MichaelNeas/3dhydra/assets/img/Daniel_DeMarco_Profile_Img.jpg

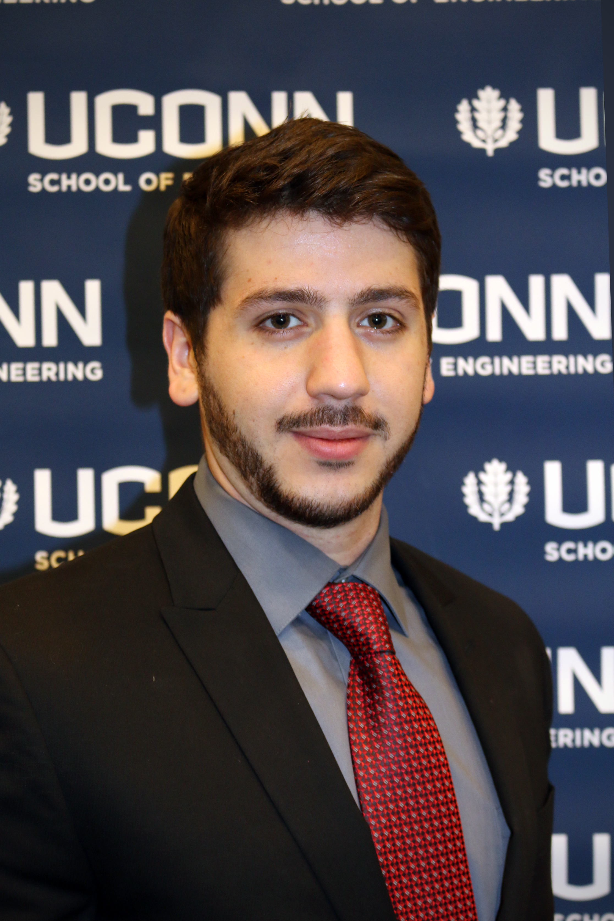
assets/img/Daniel_DeMarco_Profile_Img.jpg
