MichaelNeas/3dhydra/assets/img/Ted_Jenson_Profile_Img.jpg

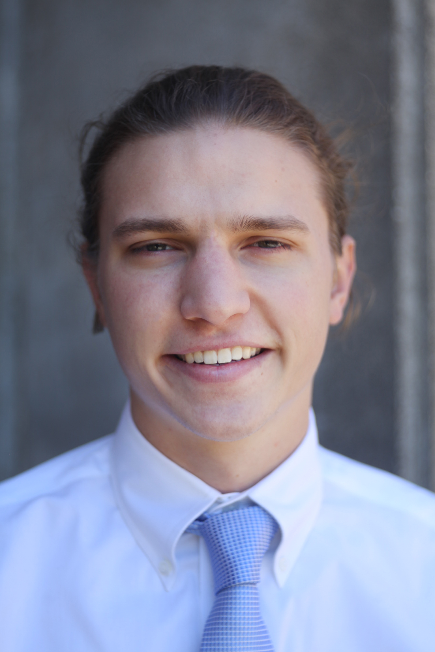
assets/img/Ted_Jenson_Profile_Img.jpg
