MichaelNeas/3dhydra/assets/stl/Hydra_-_middle_ringFingers-1_distal_middle-1.STL

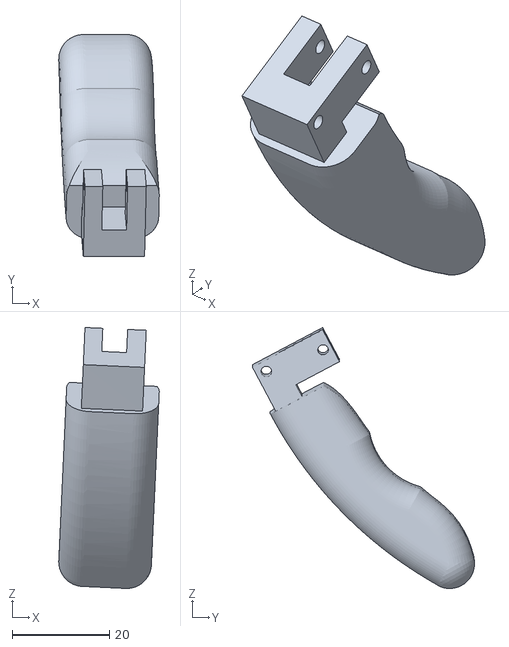
[picture p31: CAD file, 2016-04-29]
assets/stl/Hydra_-_middle_ringFingers-1_distal_middle-1.STL
20.7 x 45.6 x 53.6
