MichaelNeas/3dhydra/assets/stl/Hydra_-_pointerFinger-1_actuator-1.STL

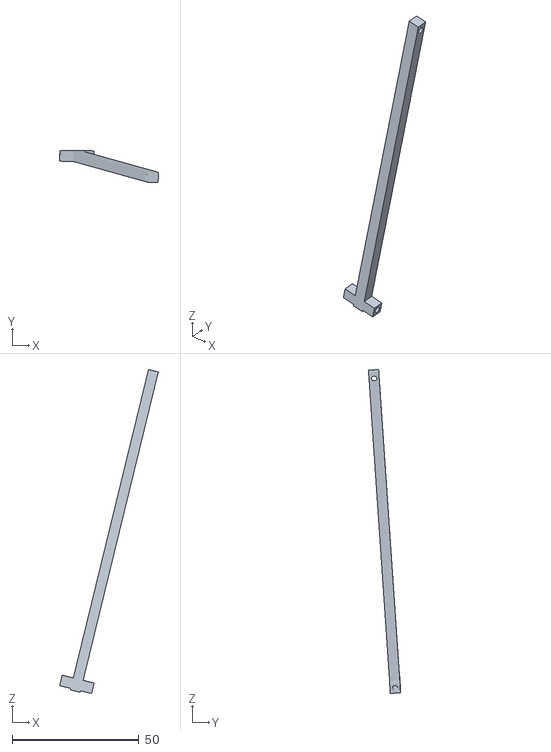
[picture p32: CAD file, 2016-04-29]
assets/stl/Hydra_-_pointerFinger-1_actuator-1.STL
38.9 x 12.6 x 127.7
