MichaelNeas/3dhydra/assets/stl/Hydra_-_middle_ringFingers-1_fingerREDUX-1.STL

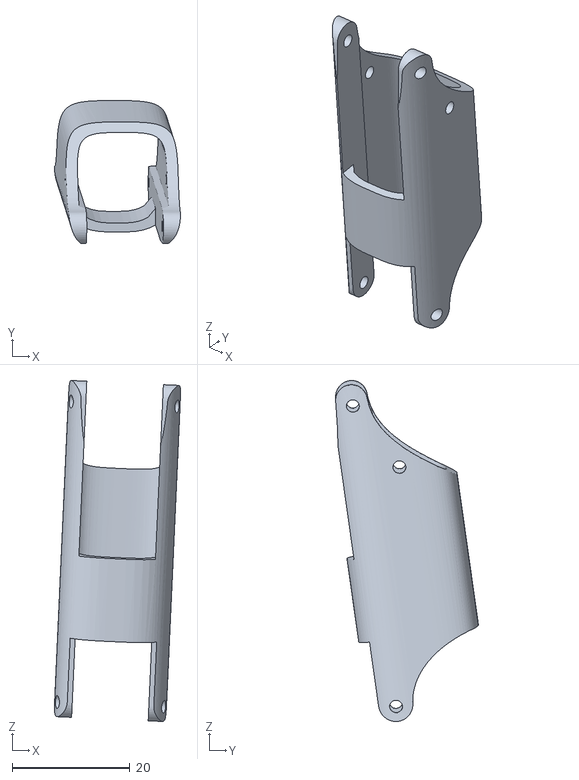
[picture p33: CAD file, 2016-04-29]
assets/stl/Hydra_-_middle_ringFingers-1_fingerREDUX-1.STL
21.4 x 24.2 x 57.8
