MichaelNeas/3dhydra/assets/stl/Hydra_-_pinkFinger-1_pinkyDM-1.STL

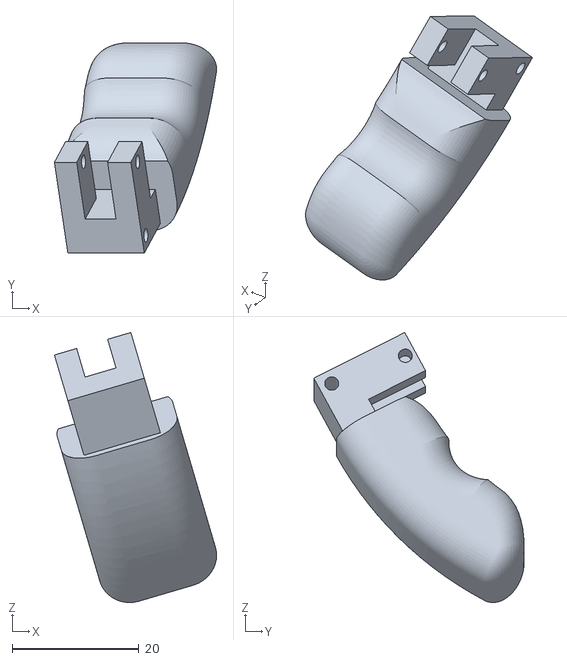
[picture p34: CAD file, 2016-04-29]
assets/stl/Hydra_-_pinkFinger-1_pinkyDM-1.STL
25.6 x 33.3 x 42.7
