MichaelNeas/3dhydra/assets/stl/Hydra_-_HydraForeArm-2_RackandPinion-1_ServoModel-1.STL

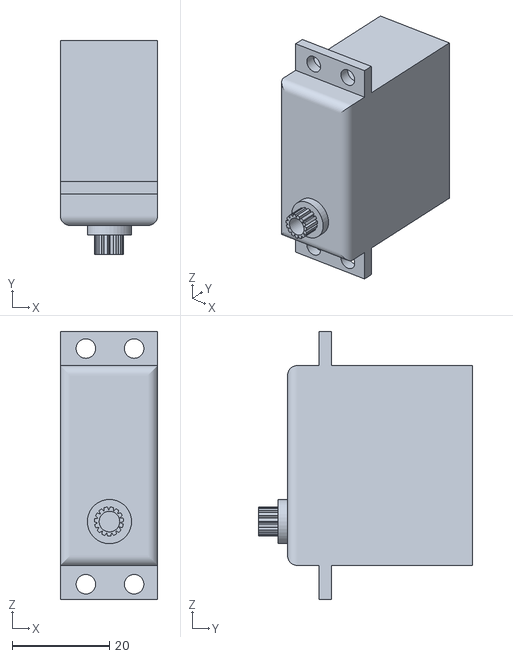
[picture p35: CAD file, 2016-04-29]
assets/stl/Hydra_-_HydraForeArm-2_RackandPinion-1_ServoModel-1.STL
20.0 x 44.0 x 55.0
