MichaelNeas/3dhydra/assets/stl/Hydra_-_HydraForeArm-2_arduinosHome-1.STL

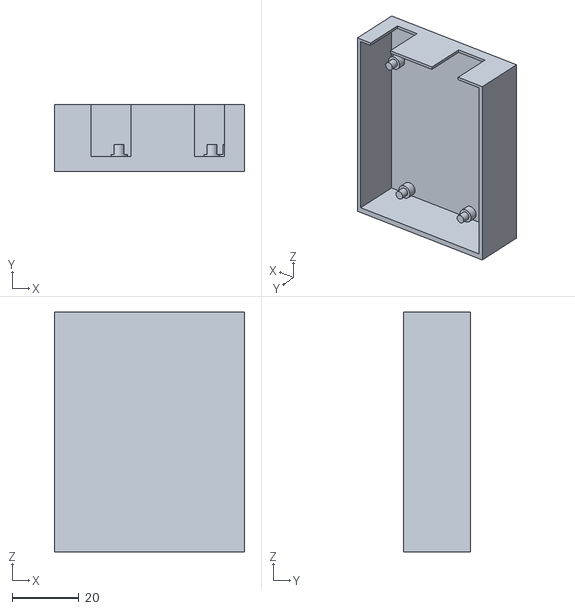
[picture p36: CAD file, 2016-04-29]
assets/stl/Hydra_-_HydraForeArm-2_arduinosHome-1.STL
57.0 x 20.0 x 72.0
