MichaelNeas/3dhydra/assets/stl/RackandPinion.STL

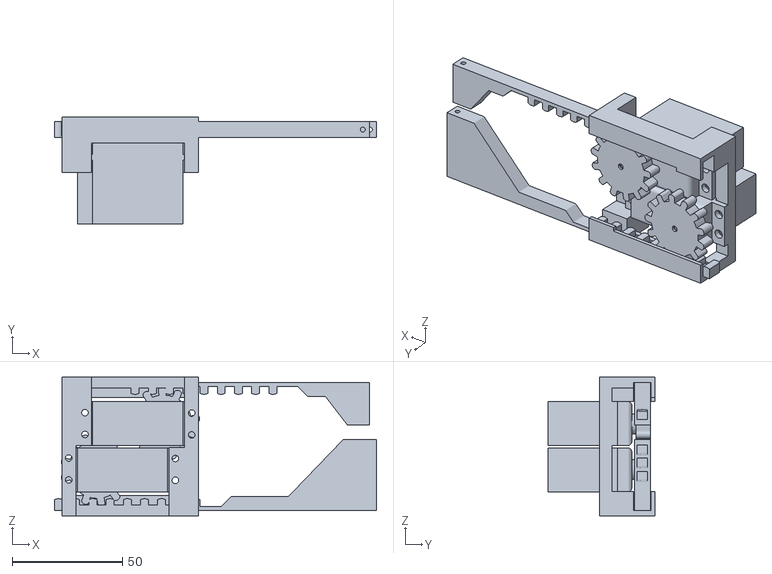
[picture p37: CAD file, 2016-04-29]
assets/stl/RackandPinion.STL
146.0 x 48.4 x 63.0
