MichaelNeas/3dhydra/assets/stl/Hydra_-_middle_ringFingers-1_middleActuator-1.STL

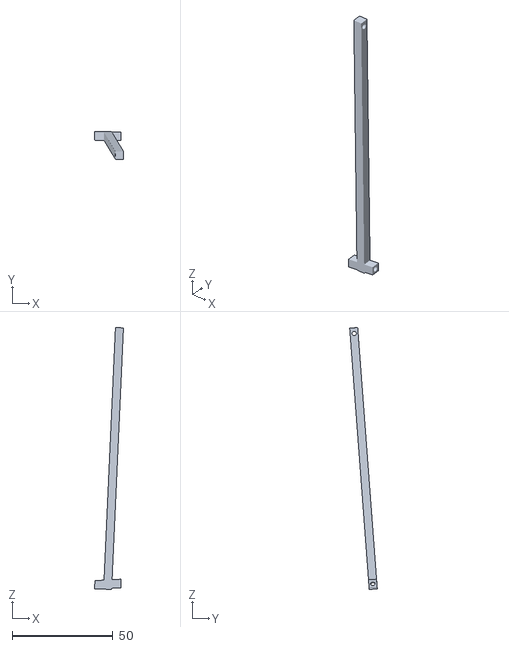
[picture p38: CAD file, 2016-04-29]
assets/stl/Hydra_-_middle_ringFingers-1_middleActuator-1.STL
14.4 x 13.7 x 130.0
