MichaelNeas/3dhydra/assets/stl/Hydra_-_HandKnuckleCombine-1_palm-1.STL

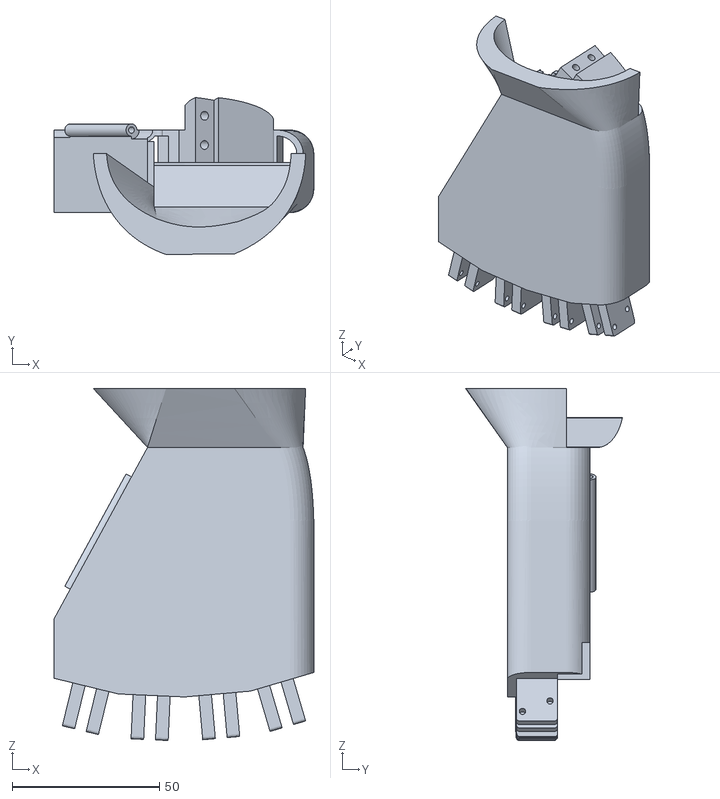
[picture p39: CAD file, 2016-04-29]
assets/stl/Hydra_-_HandKnuckleCombine-1_palm-1.STL
88.0 x 53.2 x 119.3
