MichaelNeas/3dhydra/assets/stl/HydraForeArmtogether.STL

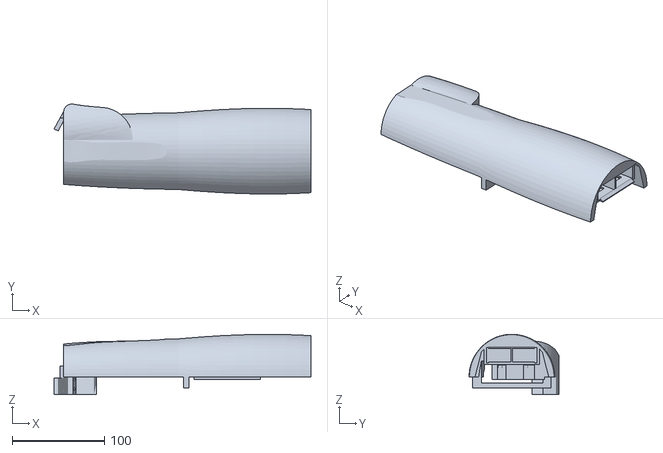
[picture p40: CAD file, 2016-04-29]
assets/stl/HydraForeArmtogether.STL
278.5 x 97.5 x 65.4
