MichaelNeas/3dhydra/assets/stl/Hydra_-_HydraForeArm-2_RackandPinion-1_servoRail-1.STL

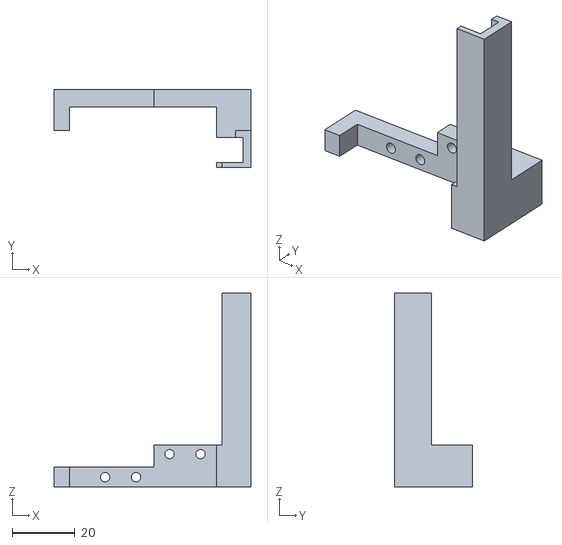
[picture p41: CAD file, 2016-04-29]
assets/stl/Hydra_-_HydraForeArm-2_RackandPinion-1_servoRail-1.STL
63.0 x 25.0 x 61.9
