MichaelNeas/3dhydra/assets/stl/ringFinger.STL

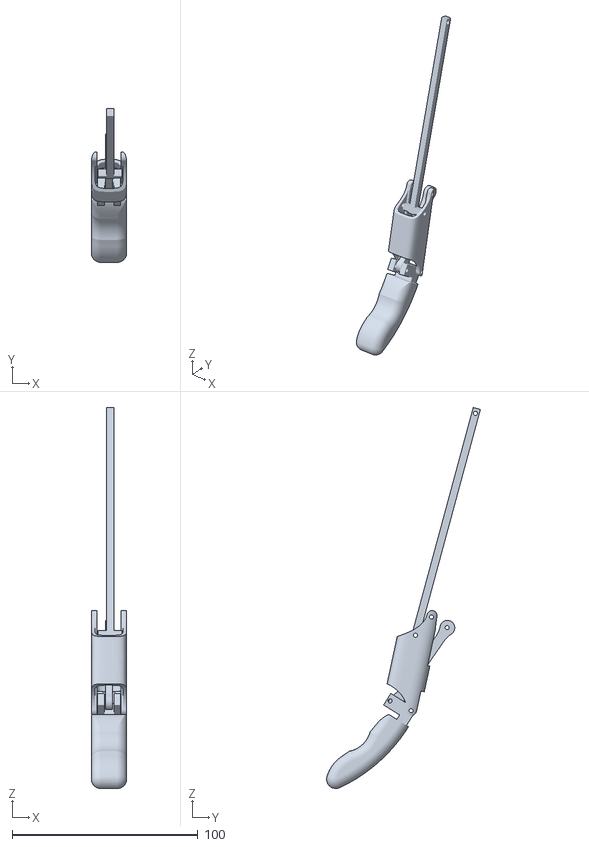
[picture p42: CAD file, 2016-04-29]
assets/stl/ringFinger.STL
19.1 x 82.8 x 205.0
