MichaelNeas/3dhydra/img/handforearmside.jpg

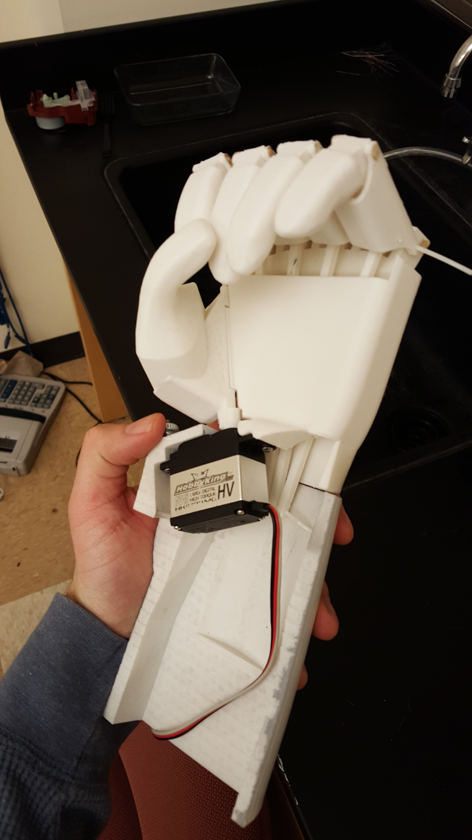
img/handforearmside.jpg
